dpelgrift/ISS-Tracker/iss-tracker/arduino_secrets.h

/* 
 arduino_secrets.h - Place to insert sensitive data
    If you fork this code be absolutely sure to not push this file with filled-in fields to keep from doxxing yourself :)
 */

// Wifi SSID and Password
// Place your Wifi SSID and password below
#define SECRET_SSID ""
#define SECRET_PASS ""

// Pedestal Lat/Lon
// Insert your pedestal latitude and longitude below (in decimal degrees)
#define SECRET_LAT 0.0f
#define SECRET_LON 0.0f
